zgcik/ballbot/runs/detect/train7/labels.jpg

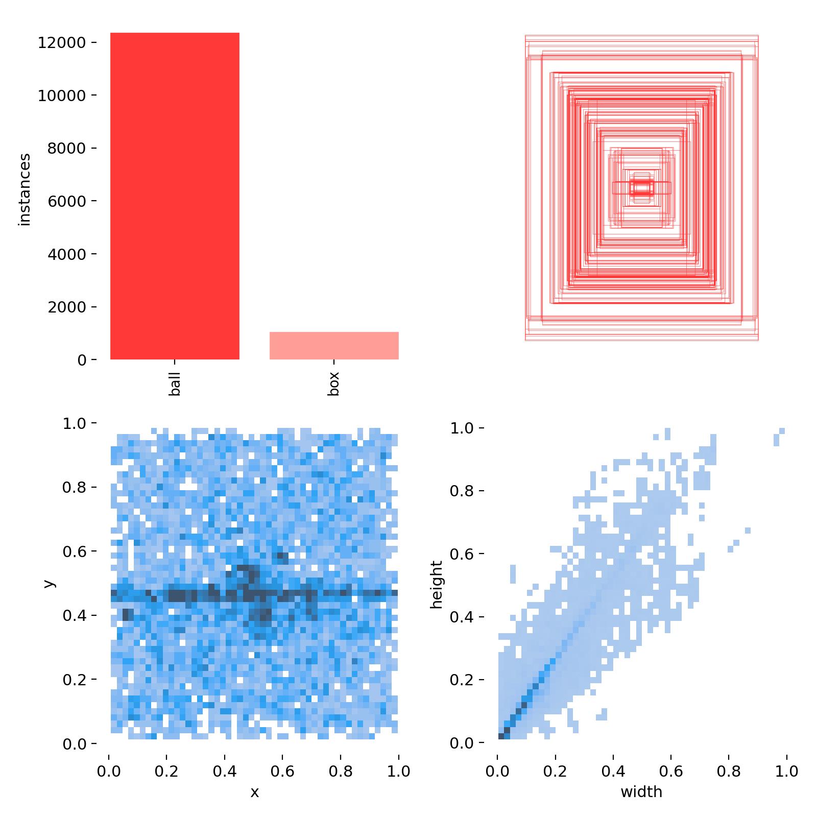
runs/detect/train7/labels.jpg
