zgcik/ballbot/runs/detect/train7/labels_correlogram.jpg

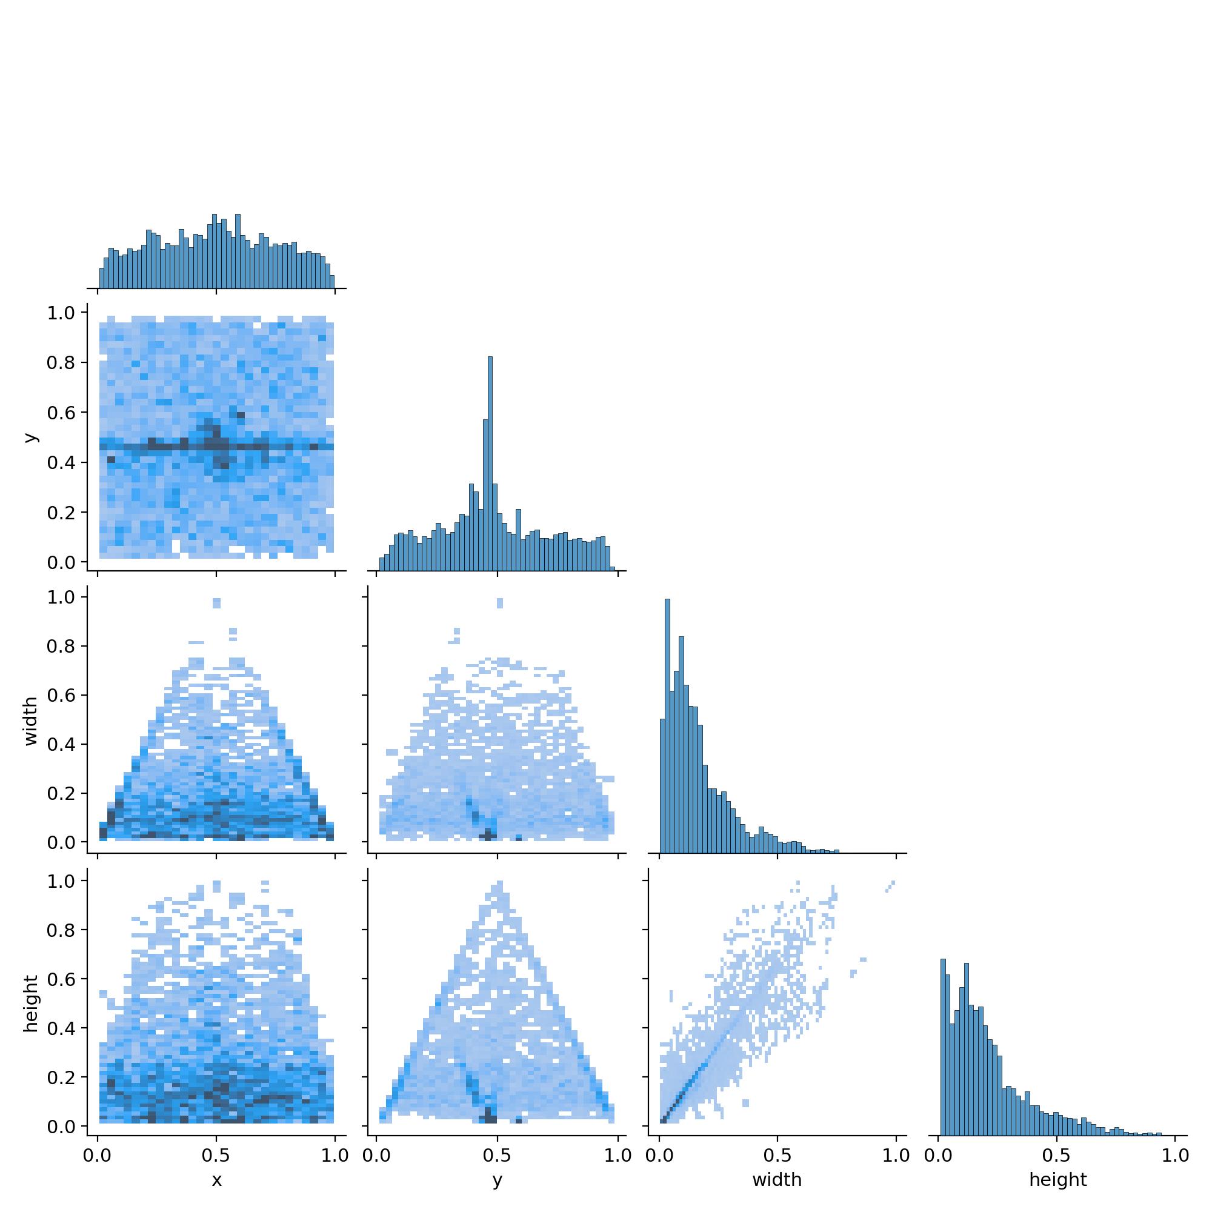
runs/detect/train7/labels_correlogram.jpg
