zgcik/ballbot/runs/detect/train7/train_batch0.jpg

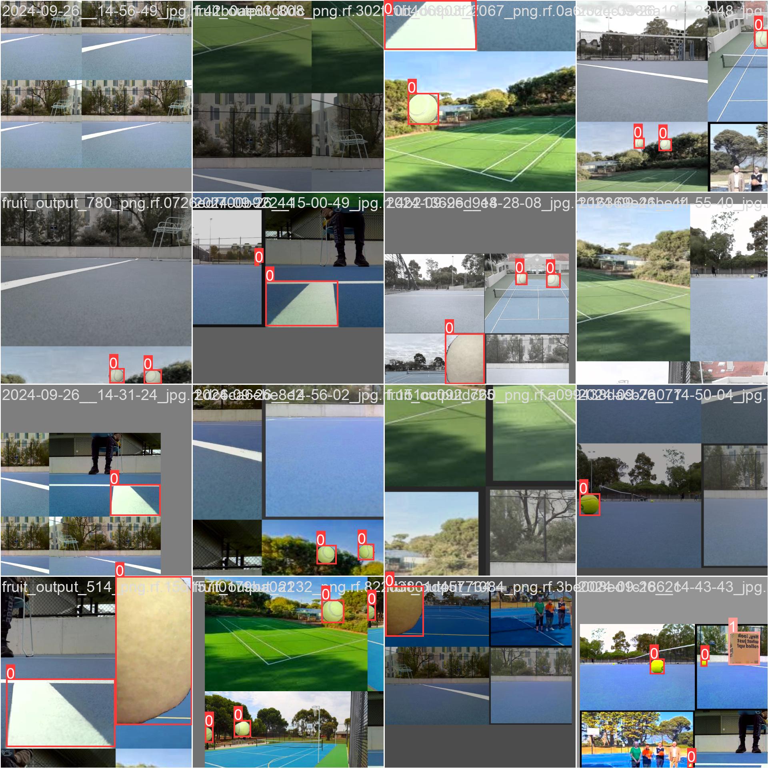
runs/detect/train7/train_batch0.jpg
