zgcik/ballbot/runs/detect/train7/train_batch2.jpg

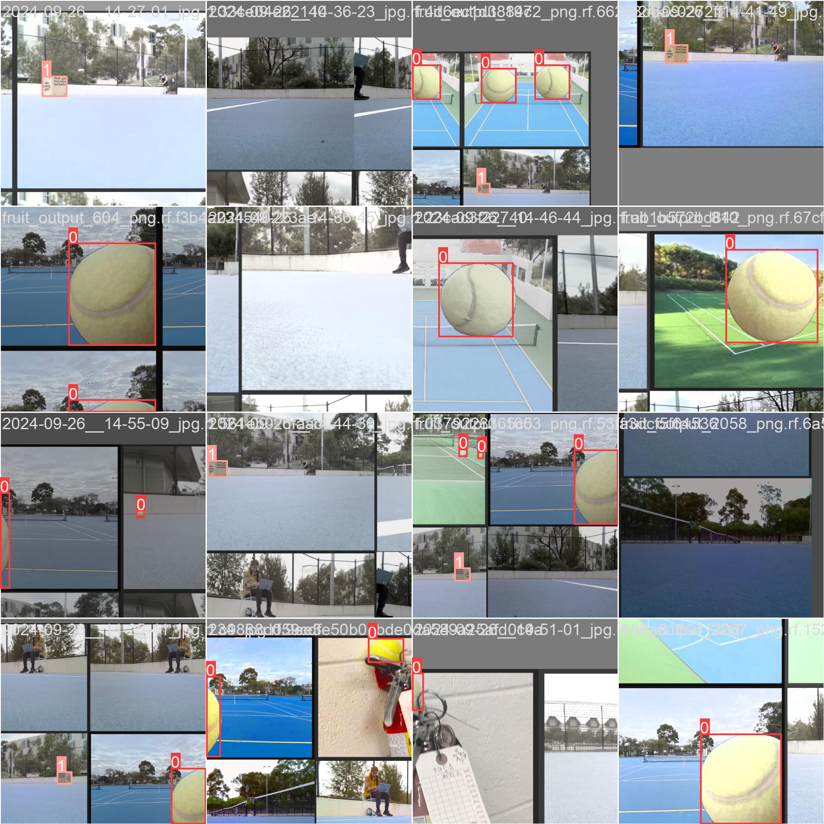
runs/detect/train7/train_batch2.jpg
