zgcik/ballbot/runs/detect/train15/confusion_matrix.png

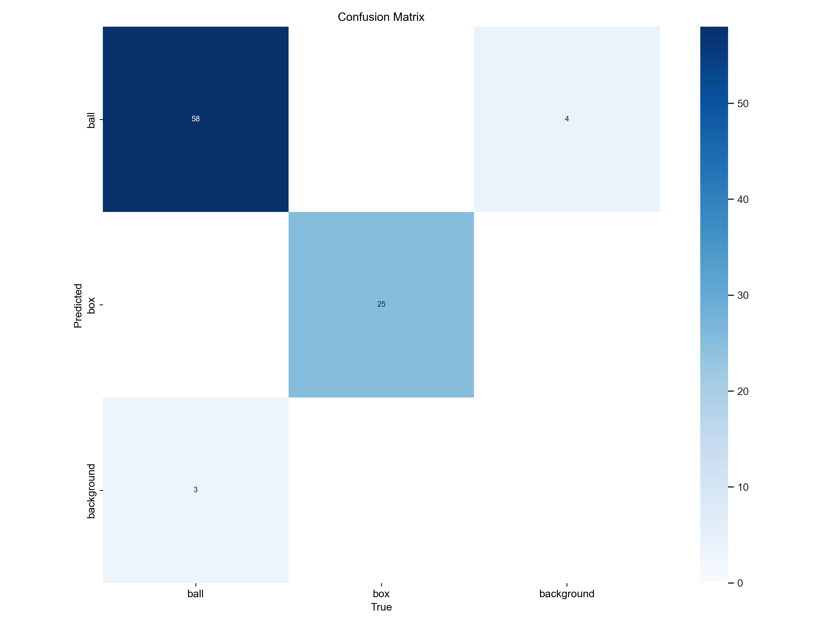
runs/detect/train15/confusion_matrix.png
