zgcik/ballbot/runs/detect/train15/confusion_matrix_normalized.png

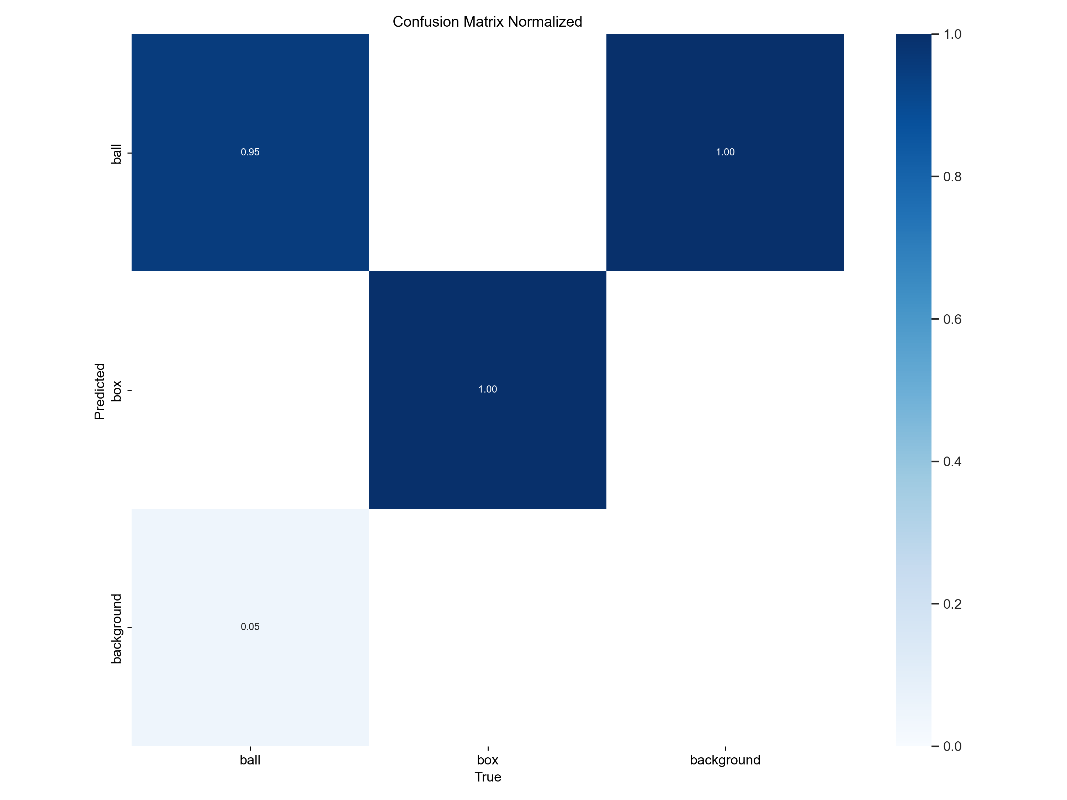
runs/detect/train15/confusion_matrix_normalized.png
