zgcik/ballbot/runs/detect/train15/F1_curve.png

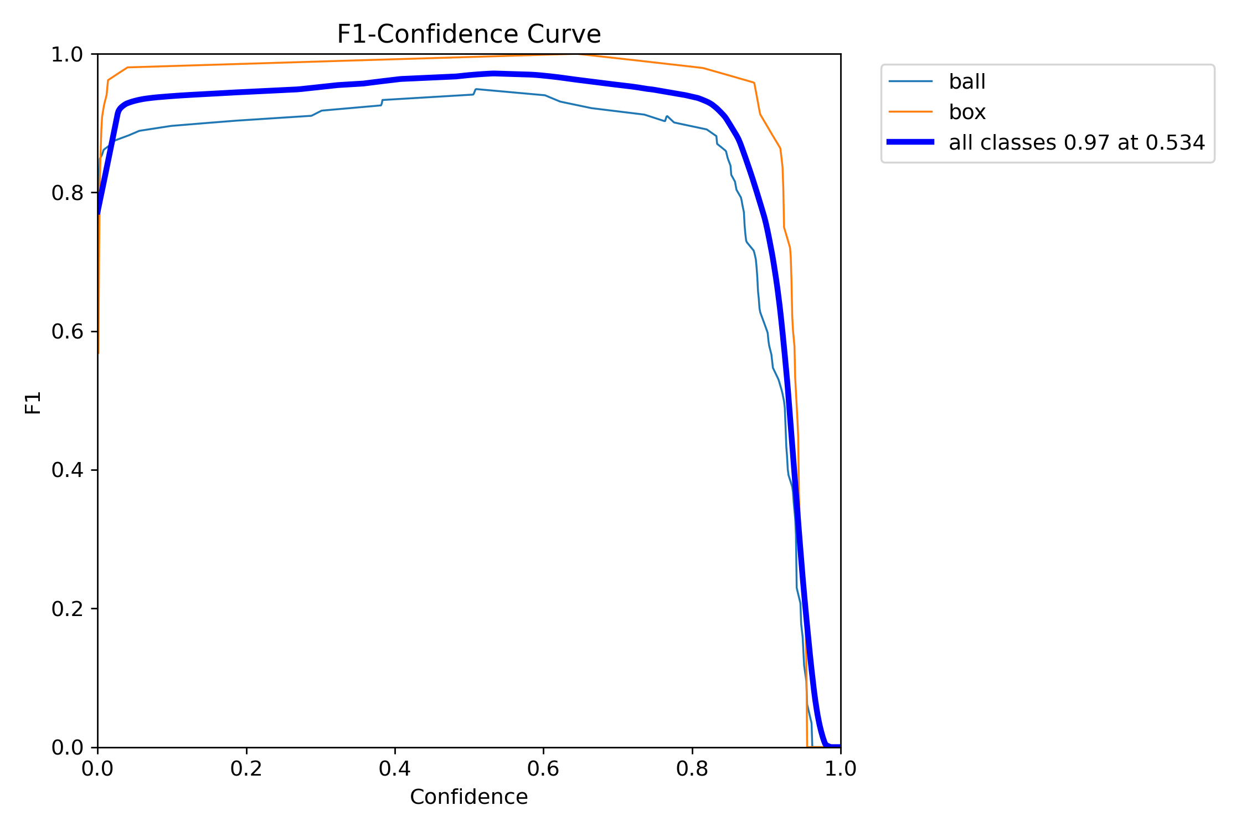
runs/detect/train15/F1_curve.png
