zgcik/ballbot/runs/detect/train15/labels.jpg

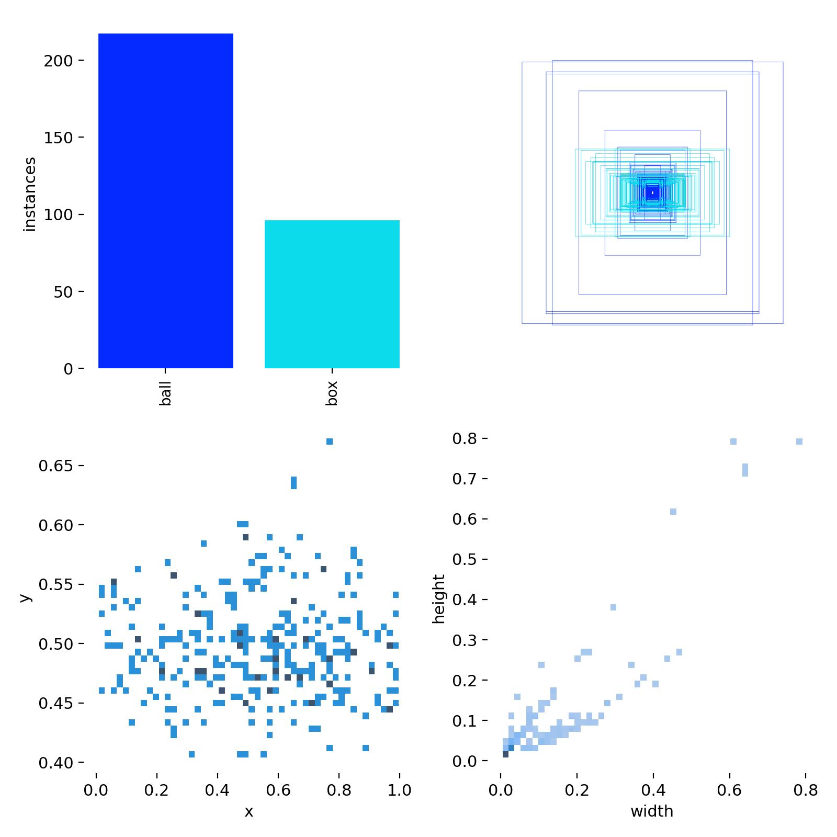
runs/detect/train15/labels.jpg
