zgcik/ballbot/runs/detect/train15/labels_correlogram.jpg

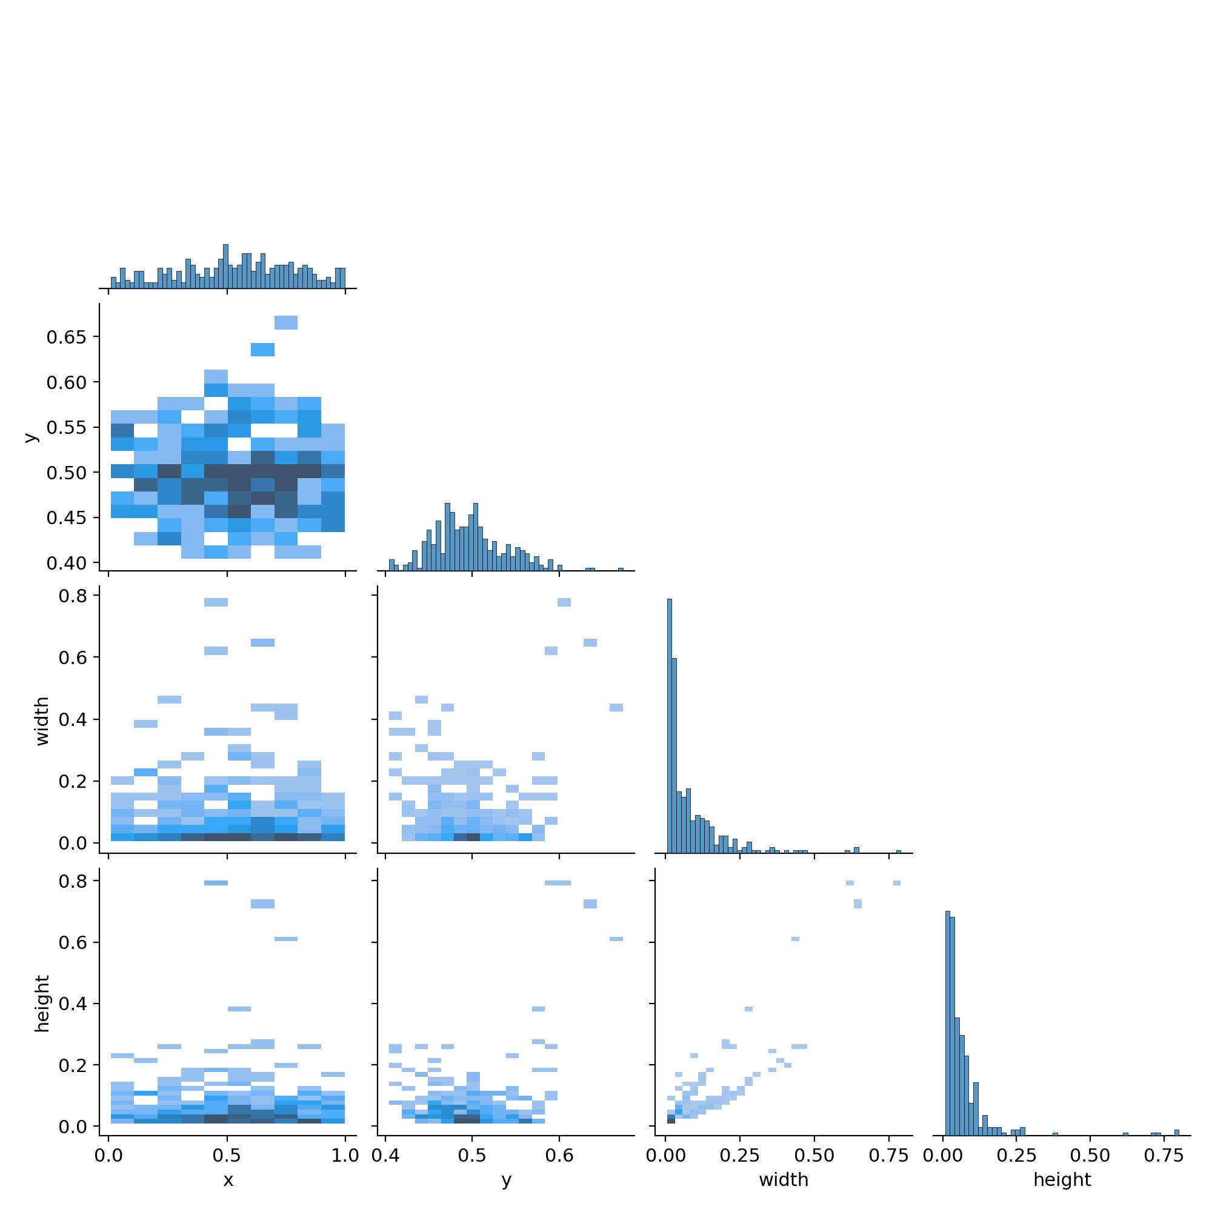
runs/detect/train15/labels_correlogram.jpg
