zgcik/ballbot/runs/detect/train15/P_curve.png

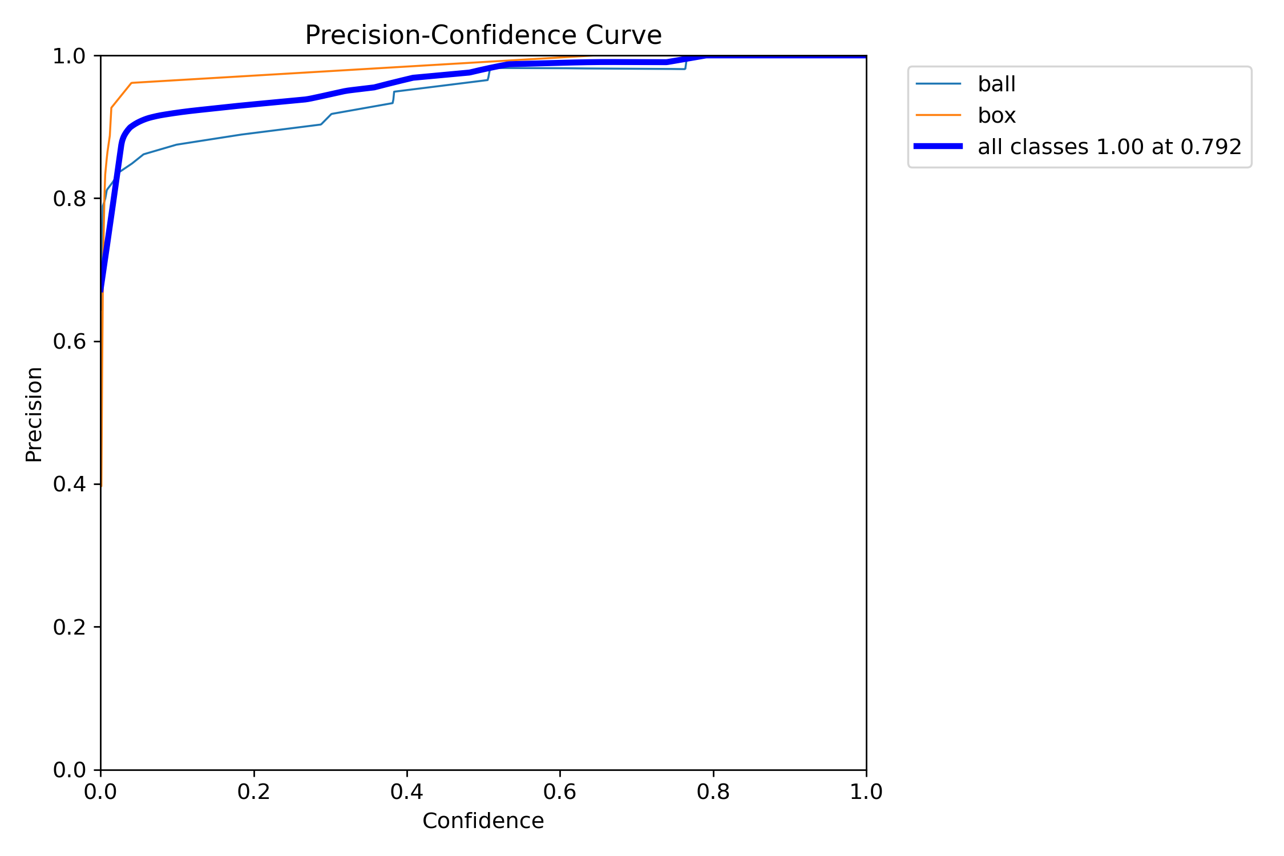
runs/detect/train15/P_curve.png
