zgcik/ballbot/runs/detect/train15/PR_curve.png

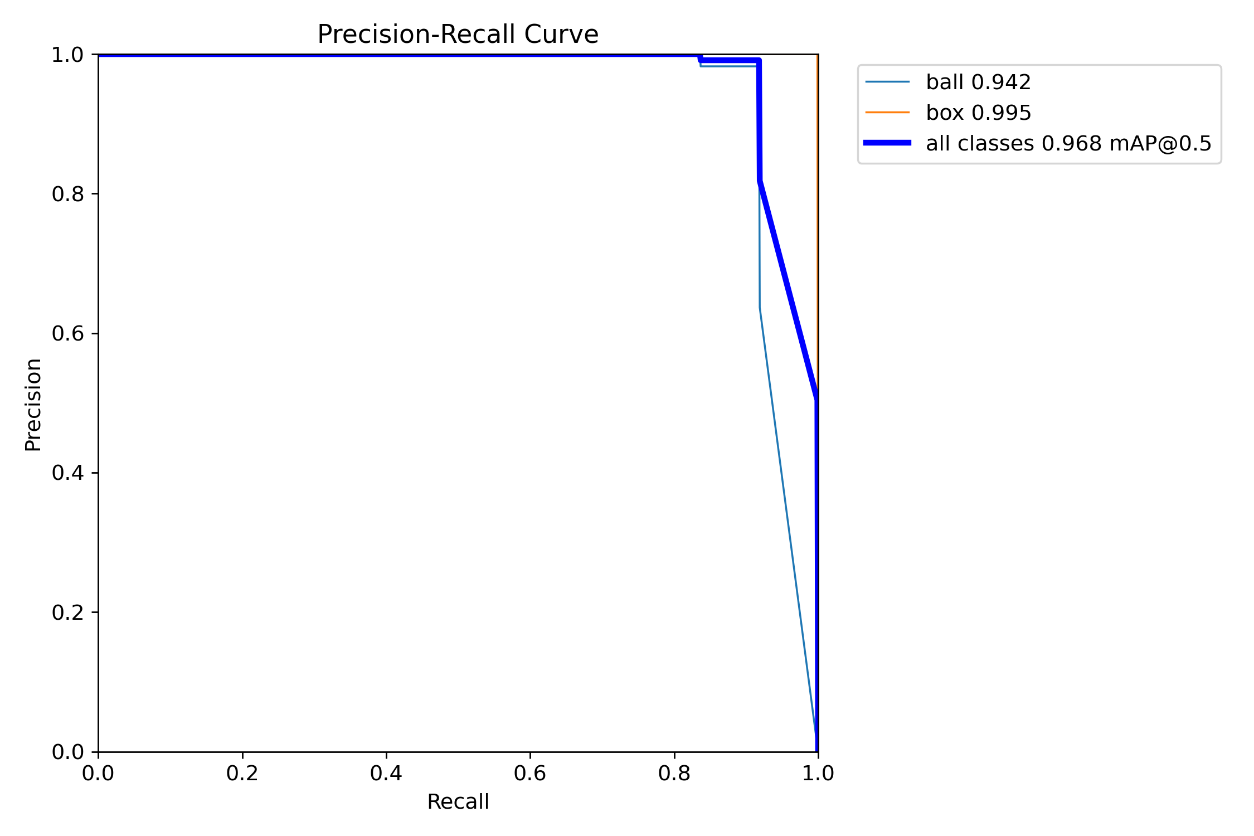
runs/detect/train15/PR_curve.png
