zgcik/ballbot/runs/detect/train15/R_curve.png

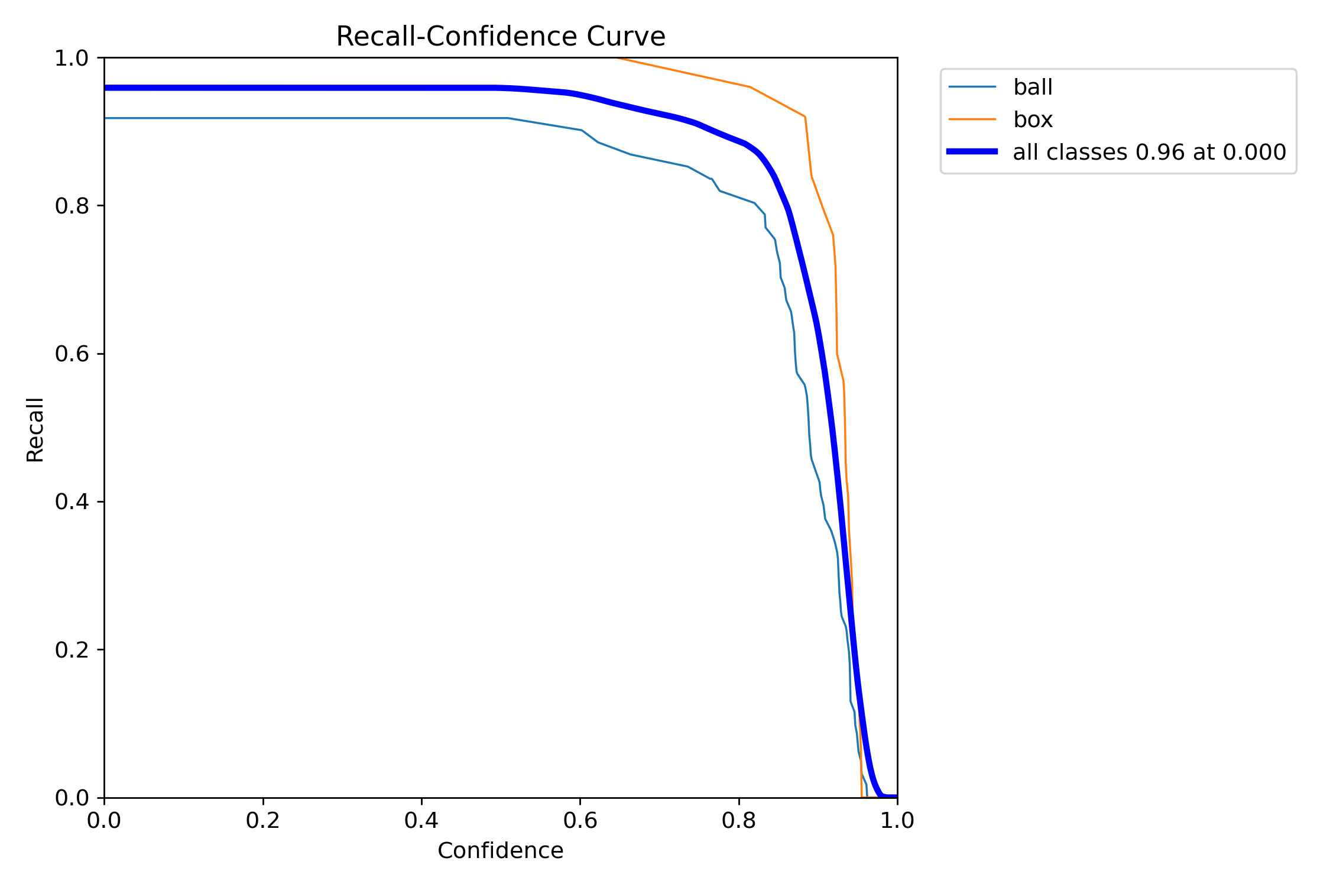
runs/detect/train15/R_curve.png
