zgcik/ballbot/runs/detect/train15/train_batch0.jpg

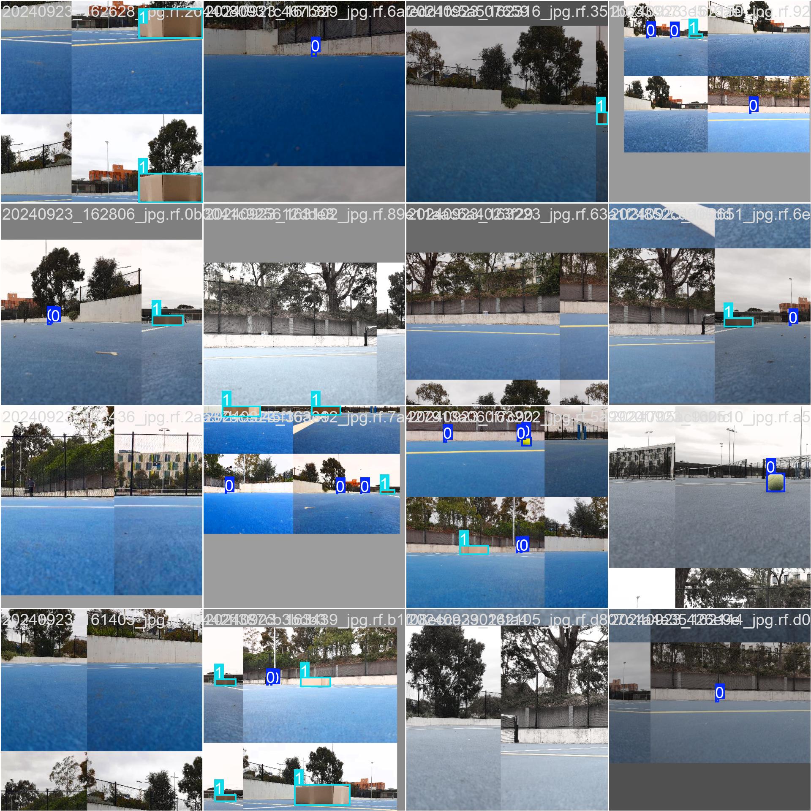
runs/detect/train15/train_batch0.jpg
