zgcik/ballbot/runs/detect/train15/train_batch1.jpg

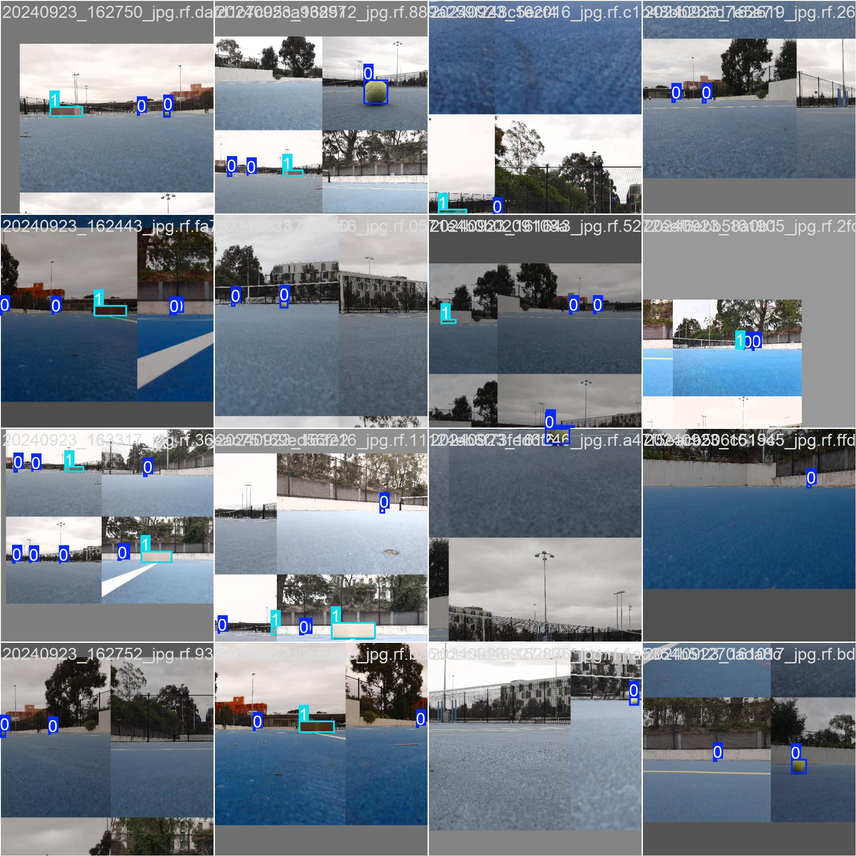
runs/detect/train15/train_batch1.jpg
