zgcik/ballbot/runs/detect/train15/train_batch2.jpg

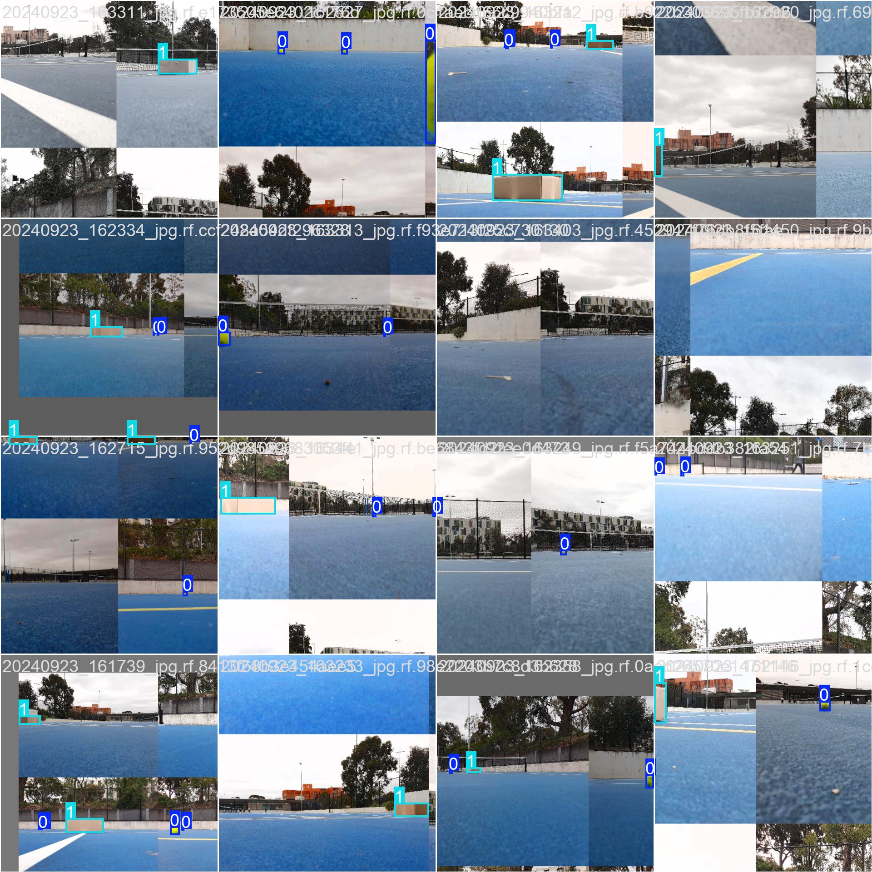
runs/detect/train15/train_batch2.jpg
