zgcik/ballbot/runs/detect/train15/train_batch990.jpg

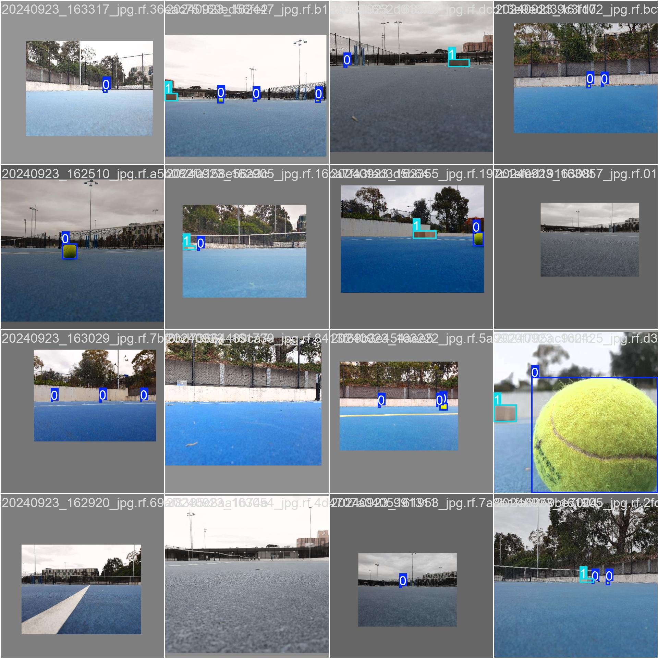
runs/detect/train15/train_batch990.jpg
