zgcik/ballbot/runs/detect/train15/train_batch991.jpg

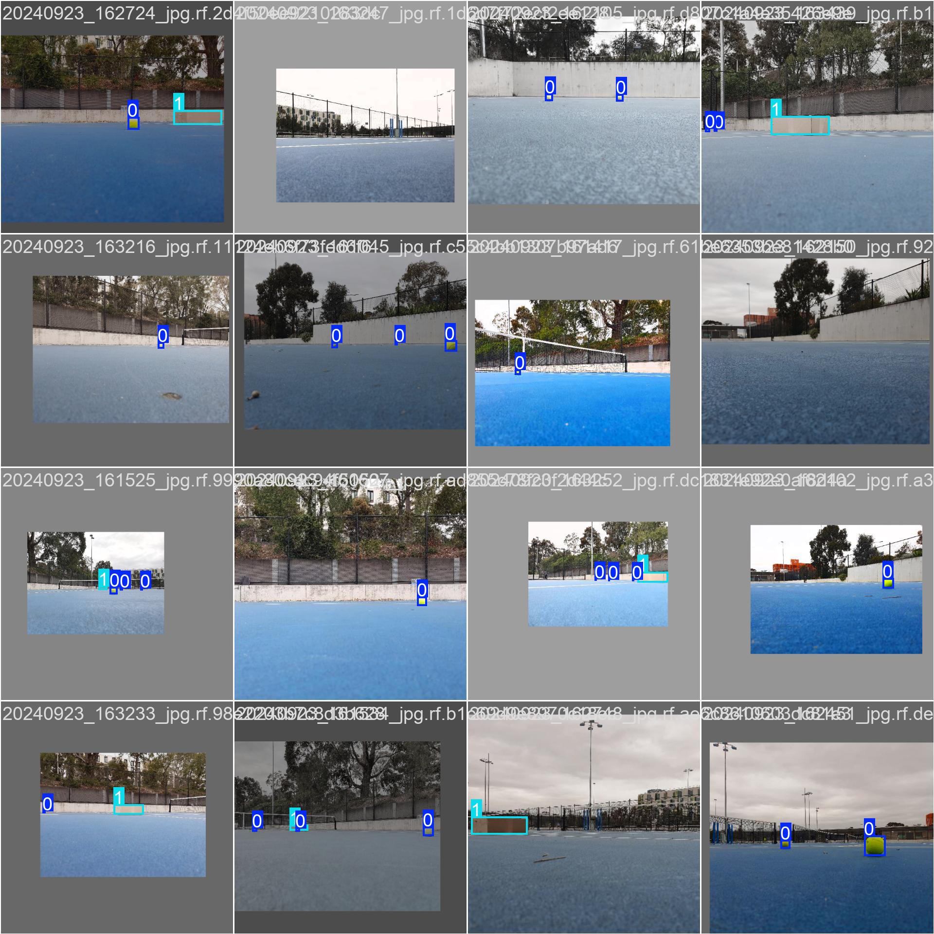
runs/detect/train15/train_batch991.jpg
