zgcik/ballbot/runs/detect/train15/train_batch992.jpg

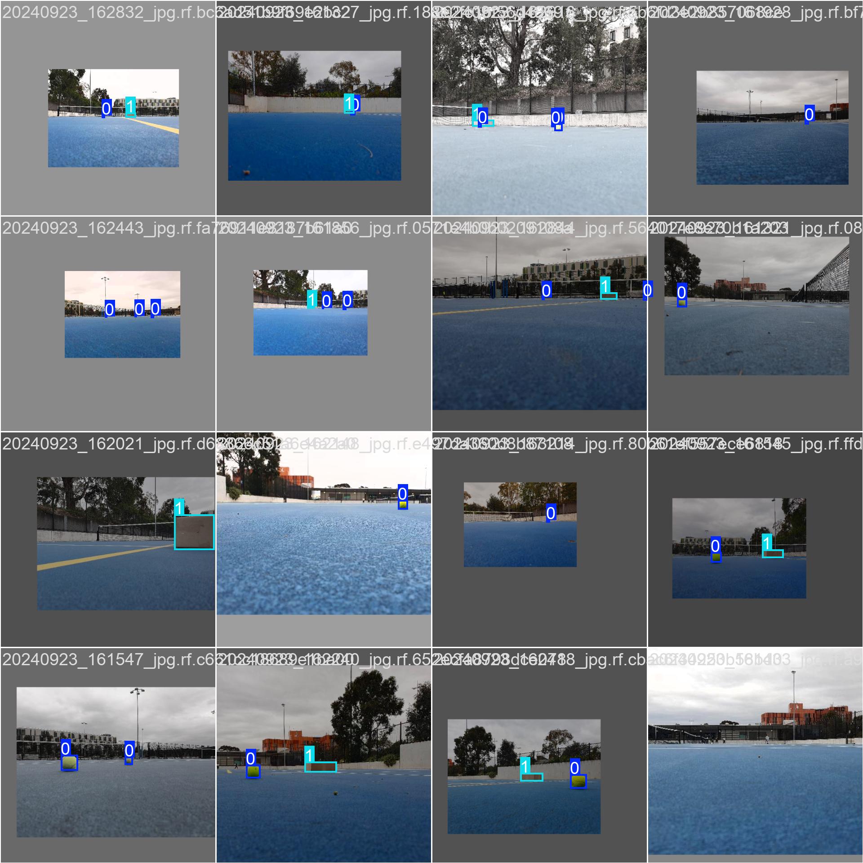
runs/detect/train15/train_batch992.jpg
