zgcik/ballbot/runs/detect/train/confusion_matrix_normalized.png

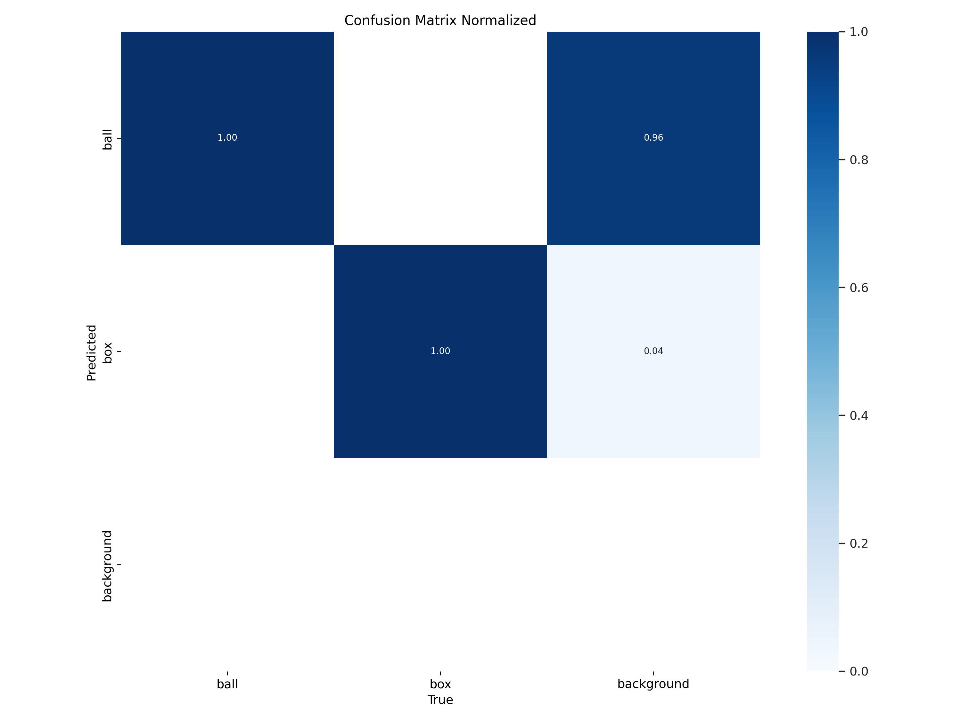
runs/detect/train/confusion_matrix_normalized.png
