zgcik/ballbot/runs/detect/train/val_batch0_labels.jpg

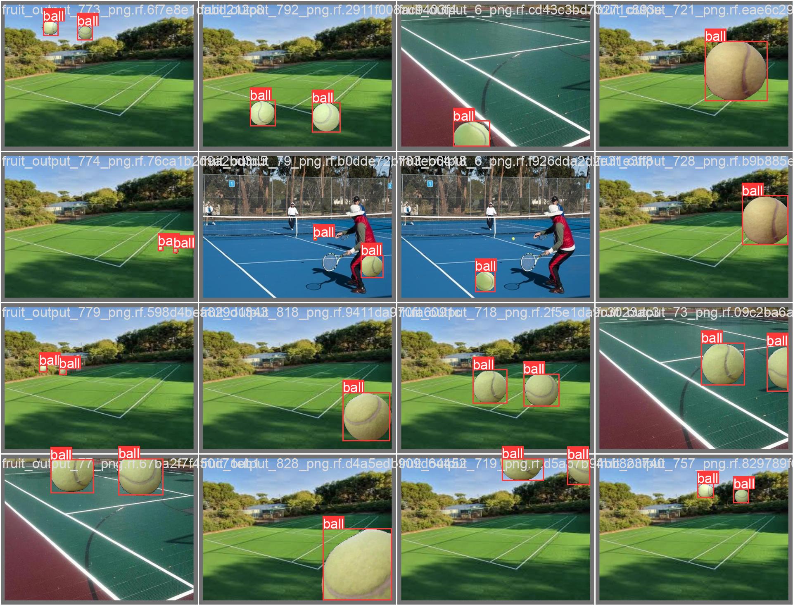
runs/detect/train/val_batch0_labels.jpg
