zgcik/ballbot/runs/detect/train/val_batch1_labels.jpg

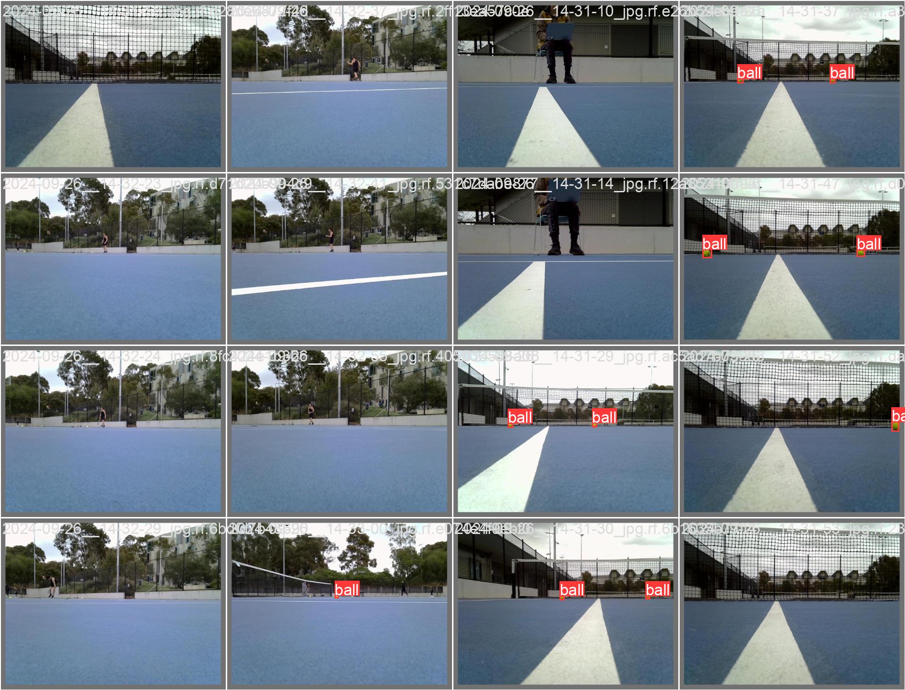
runs/detect/train/val_batch1_labels.jpg
