zgcik/ballbot/runs/detect/train/val_batch2_labels.jpg

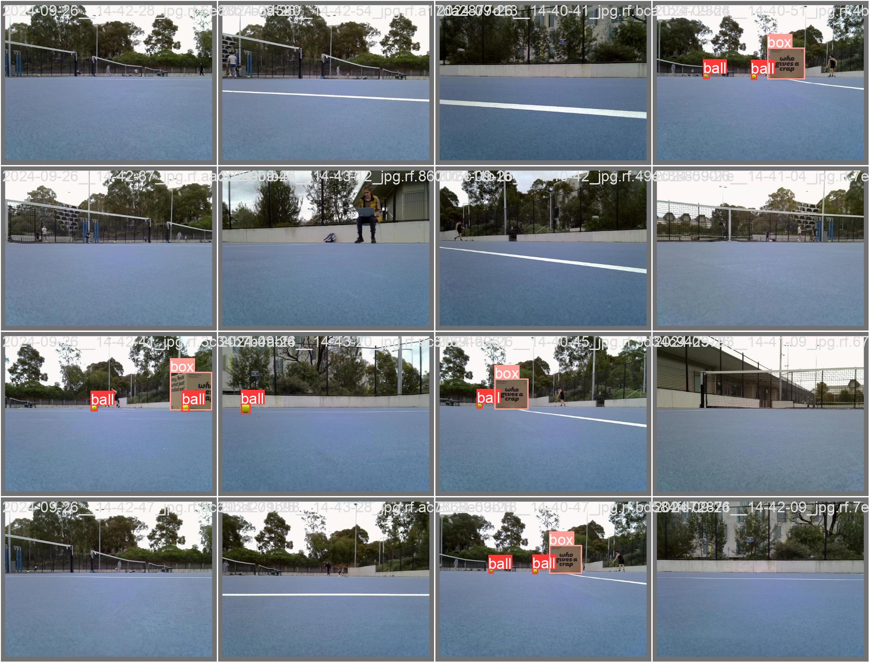
runs/detect/train/val_batch2_labels.jpg
