zgcik/ballbot/runs/detect/train15/results.png

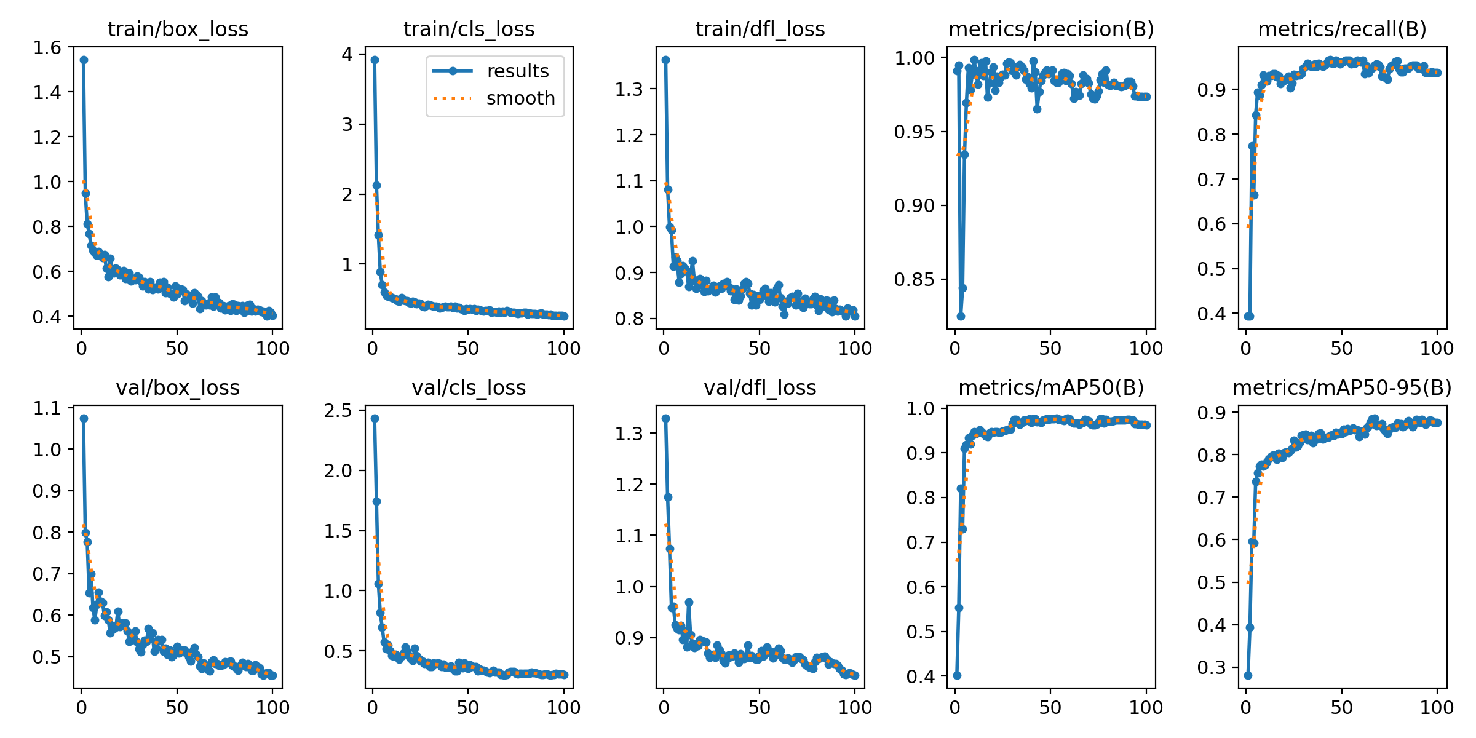
runs/detect/train15/results.png
