zgcik/ballbot/runs/detect/train/results.png

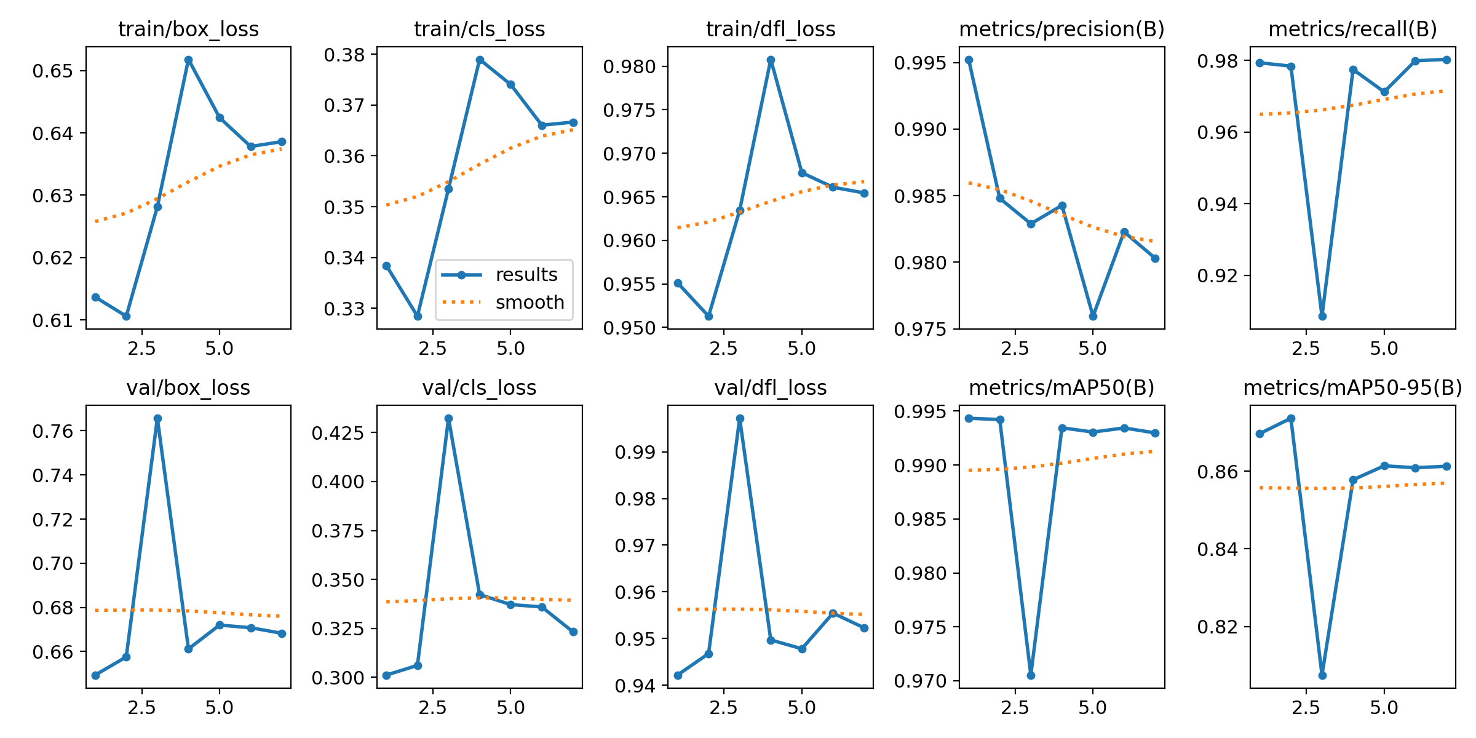
runs/detect/train/results.png
